Helge-Stein-Group/AutoBASS/Mechanical Parts/Electrolyte Tap/Motor_Case_Part1.stl

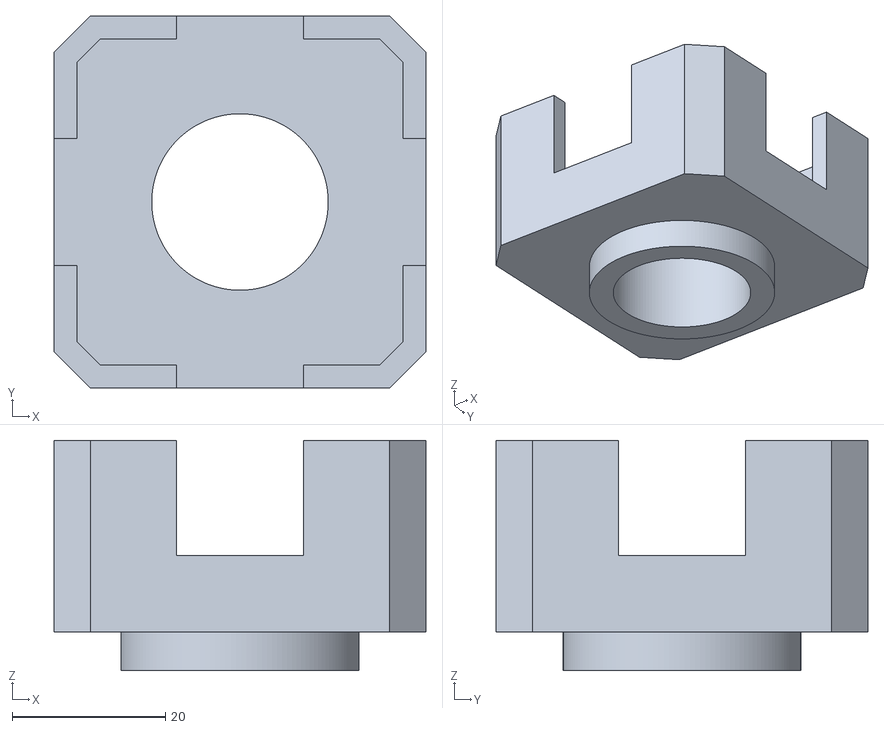
[picture p17: CAD file, 2022-05-20]
Mechanical Parts/Electrolyte Tap/Motor_Case_Part1.stl
48.5 x 48.5 x 30.0
