Helge-Stein-Group/AutoBASS/Mechanical Parts/Robots/Robot A/LeftFinger.stl

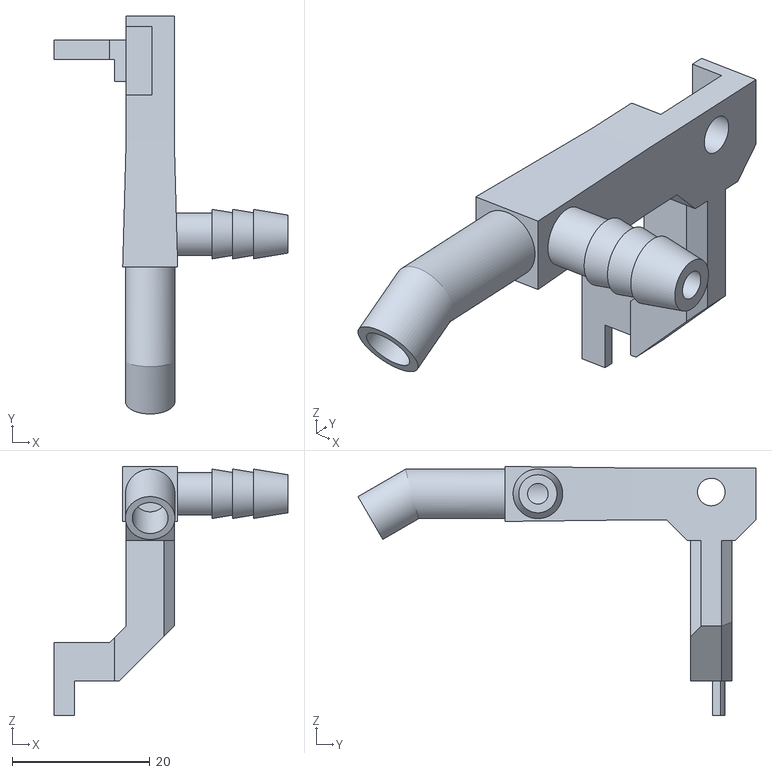
[picture p18: CAD file, 2022-05-20]
Mechanical Parts/Robots/Robot A/LeftFinger.stl
34.0 x 57.9 x 36.2
