Helge-Stein-Group/AutoBASS/Mechanical Parts/Robots/Robot B/RightGripper.stl

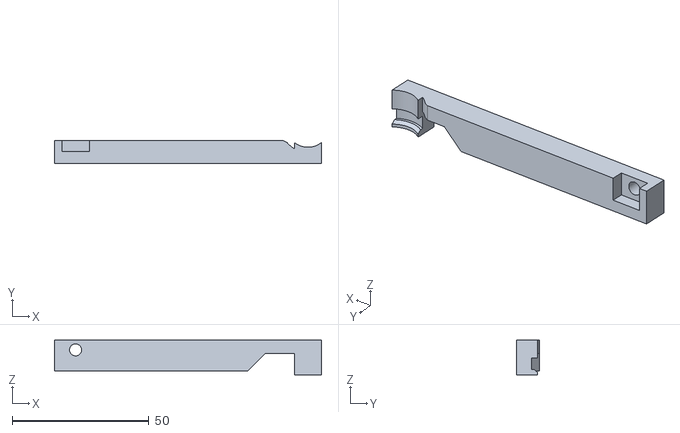
[picture p19: CAD file, 2022-05-20]
Mechanical Parts/Robots/Robot B/RightGripper.stl
97.5 x 8.50 x 12.8
