Helge-Stein-Group/AutoBASS/Mechanical Parts/Tray/Optical pole adapter.stl

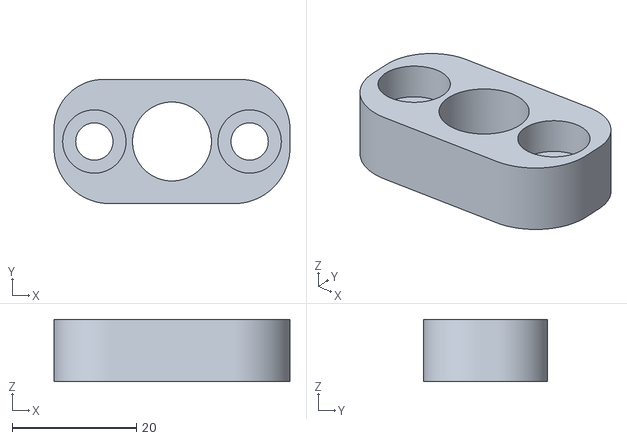
[picture p20: CAD file, 2022-05-20]
Mechanical Parts/Tray/Optical pole adapter.stl
38.0 x 20.0 x 10.0
