Helge-Stein-Group/AutoBASS/Mechanical Parts/Electrolyte Tap/Arm_Part2.stl

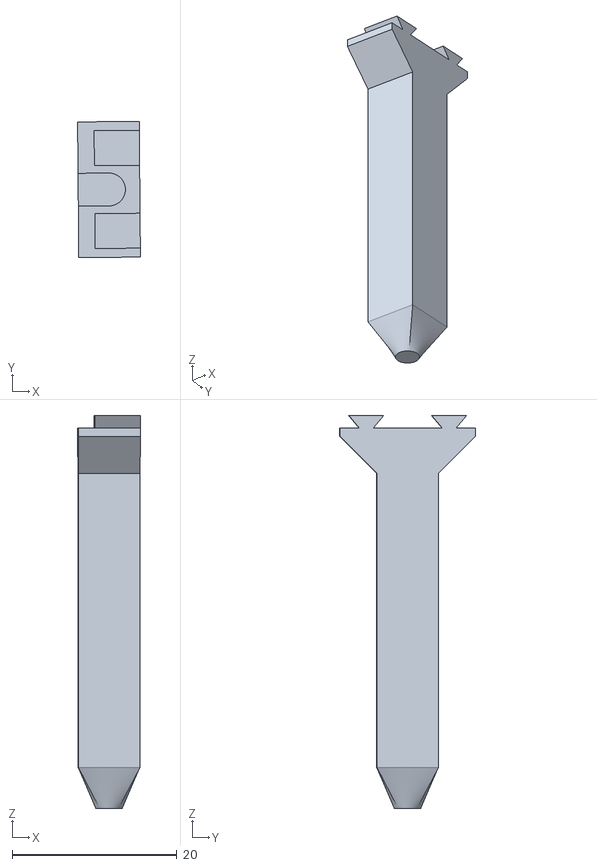
[picture p21: CAD file, 2022-05-20]
Mechanical Parts/Electrolyte Tap/Arm_Part2.stl
7.64 x 16.6 x 47.8
