Helge-Stein-Group/AutoBASS/Mechanical Parts/Electrolyte Tap/Shaft.stl

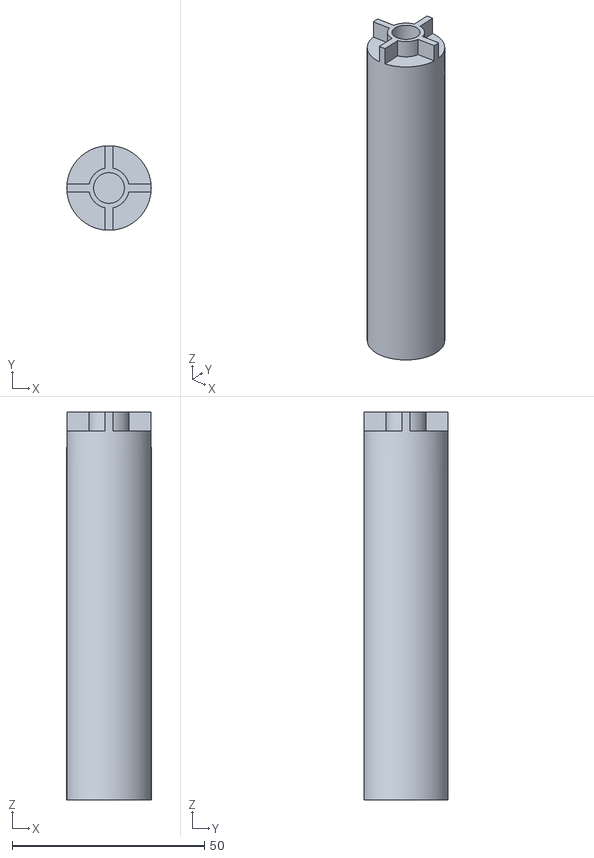
[picture p22: CAD file, 2022-05-20]
Mechanical Parts/Electrolyte Tap/Shaft.stl
22.0 x 22.0 x 101.0
