Helge-Stein-Group/AutoBASS/Mechanical Parts/Electrolyte Tap/Motor_Case_Part2.stl

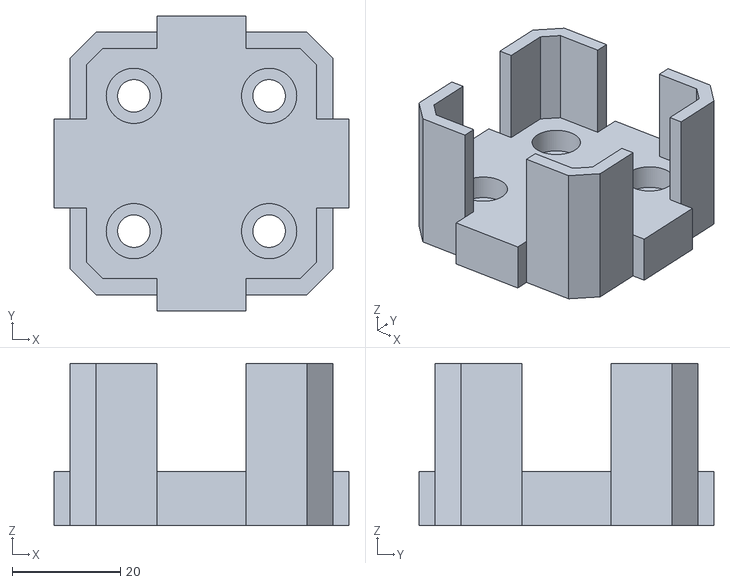
[picture p23: CAD file, 2022-05-20]
Mechanical Parts/Electrolyte Tap/Motor_Case_Part2.stl
54.5 x 54.5 x 30.0
