Helge-Stein-Group/AutoBASS/Mechanical Parts/Tray/MainBody/Separator.stl

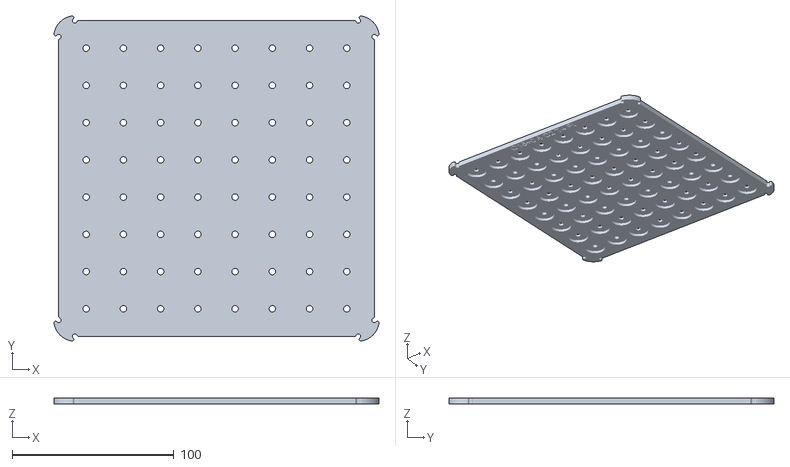
[picture p24: CAD file, 2022-05-20]
Mechanical Parts/Tray/MainBody/Separator.stl
200.8 x 200.8 x 4.00
